swift502/Krtkus/images/3.webp

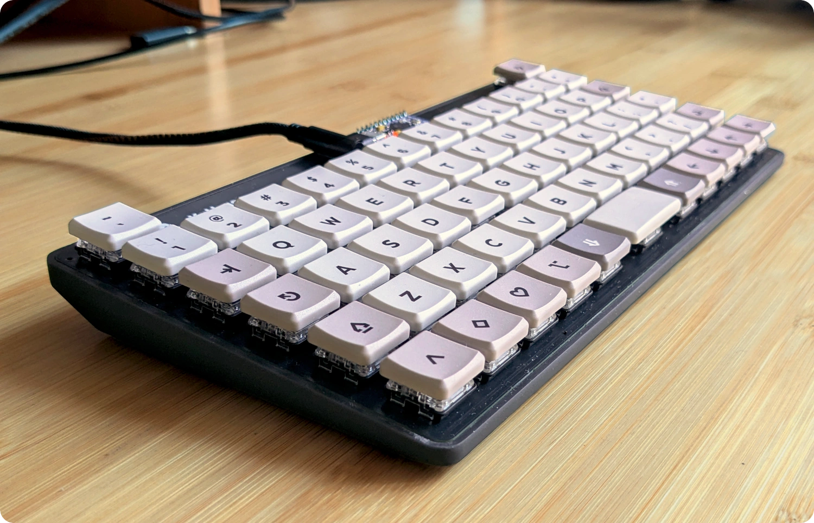
images/3.webp
